miguel-osuna/Mikeduino-Microcontroller/Design Documentation/3D Models/CAPC/CAPC4564X160N EIA 1825.step

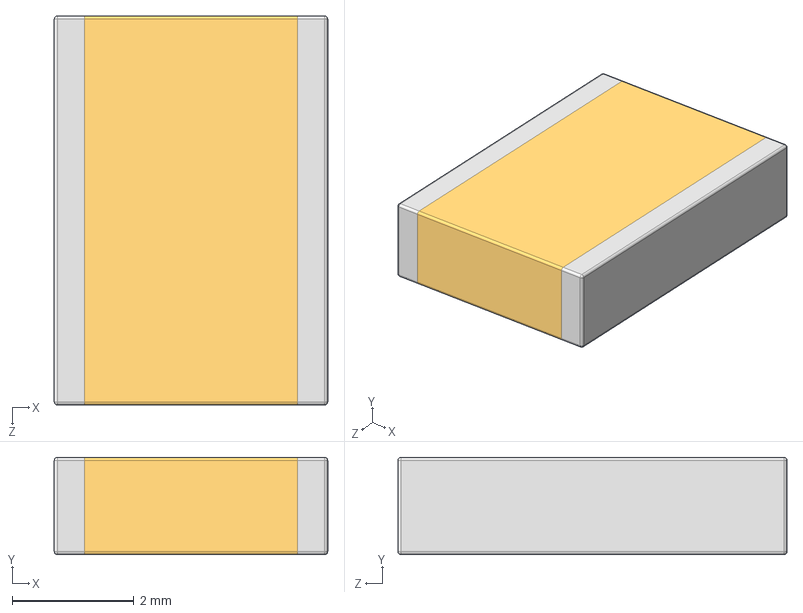
[picture p29: CAD file, 2019-04-03]
Design Documentation/3D Models/CAPC/CAPC4564X160N EIA 1825.step
4.50 x 1.60 x 6.40 mm
