miguel-osuna/Mikeduino-Microcontroller/Design Documentation/3D Models/CAPC2012X95N EIA 0805.step

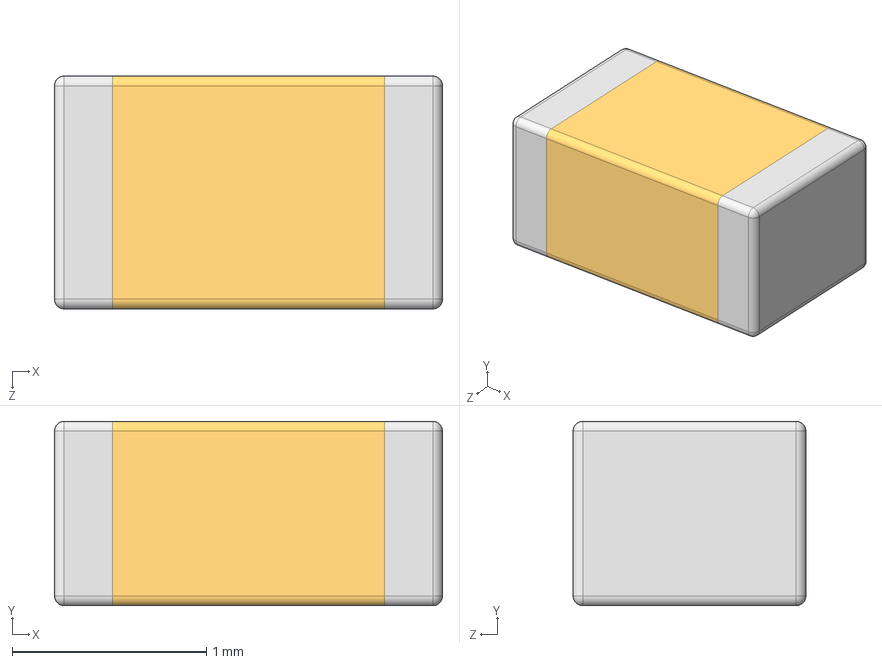
[picture p31: CAD file, 2019-04-03]
Design Documentation/3D Models/CAPC2012X95N EIA 0805.step
2.00 x 0.95 x 1.20 mm
