miguel-osuna/Mikeduino-Microcontroller/Design Documentation/3D Models/User Library-CapAluRadial_D63H70P25.step

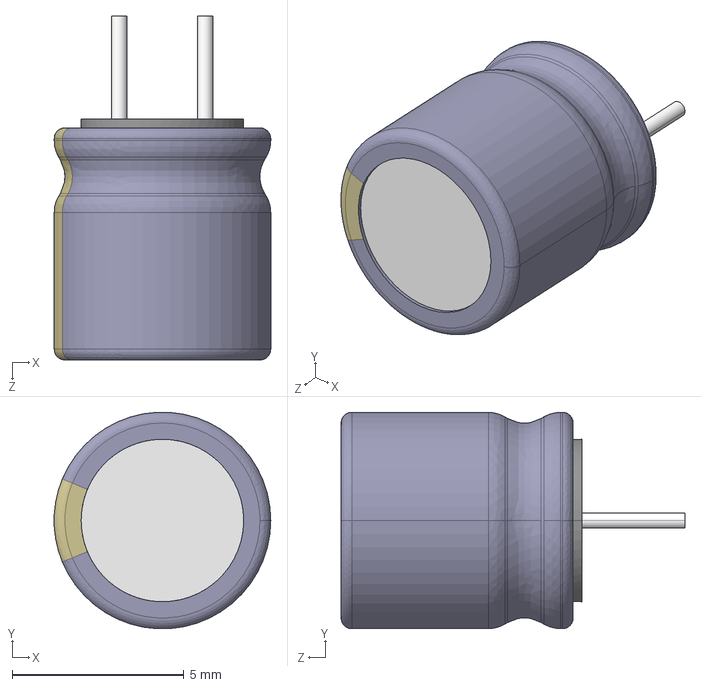
[picture p33: CAD file, 2019-04-03]
Design Documentation/3D Models/User Library-CapAluRadial_D63H70P25.step
6.30 x 6.29 x 10.0 mm
