miguel-osuna/Mikeduino-Microcontroller/Design Documentation/3D Models/HDR_1x3_White.stp

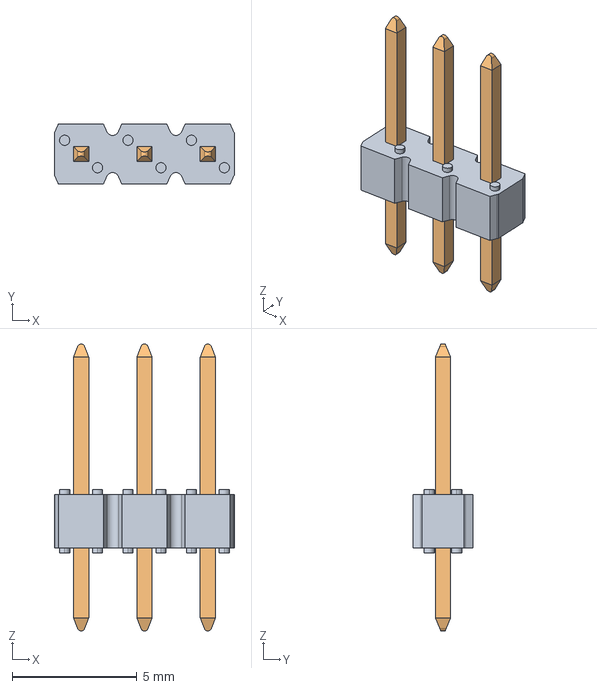
[picture p35: CAD file, 2019-04-03]
Design Documentation/3D Models/HDR_1x3_White.stp
7.22 x 2.41 x 11.5 mm
77310_Y16 x 3
