miguel-osuna/Mikeduino-Microcontroller/Design Documentation/3D Models/CAPC/CAPC4833X280N EIA 1913.step

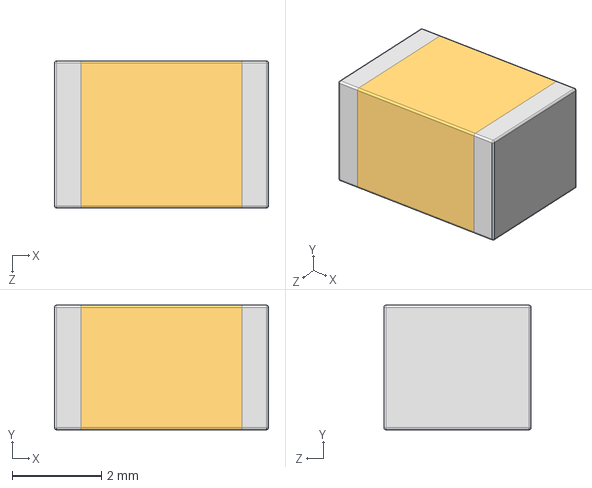
[picture p36: CAD file, 2019-04-03]
Design Documentation/3D Models/CAPC/CAPC4833X280N EIA 1913.step
4.80 x 2.80 x 3.30 mm
