miguel-osuna/Mikeduino-Microcontroller/Design Documentation/3D Models/User Library-LED SMD 0603 super red.step

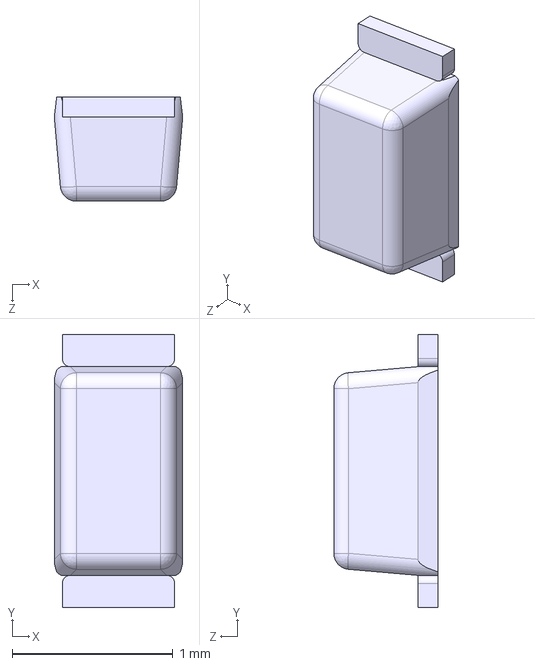
[picture p37: CAD file, 2019-04-03]
Design Documentation/3D Models/User Library-LED SMD 0603 super red.step
0.8 x 1.70 x 0.65 mm
