miguel-osuna/Mikeduino-Microcontroller/Design Documentation/3D Models/dil_socket.stp

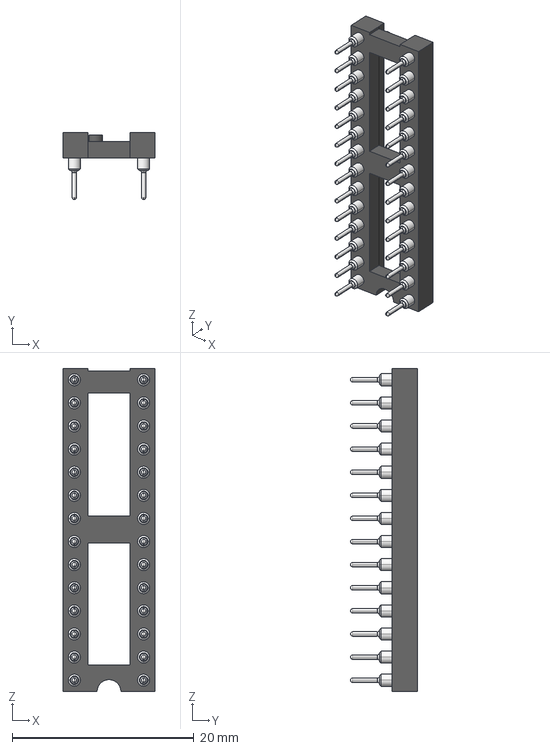
[picture p39: CAD file, 2019-04-03]
Design Documentation/3D Models/dil_socket.stp
10.1 x 7.37 x 35.5 mm
