miguel-osuna/Mikeduino-Microcontroller/Design Documentation/3D Models/HDR_1x4_White.stp

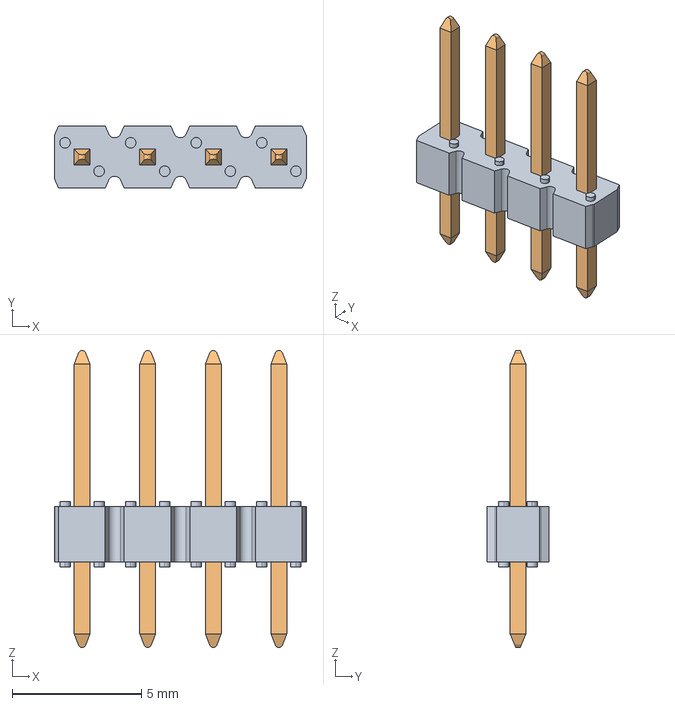
[picture p41: CAD file, 2019-04-03]
Design Documentation/3D Models/HDR_1x4_White.stp
9.76 x 2.41 x 11.5 mm
