miguel-osuna/Mikeduino-Microcontroller/Design Documentation/3D Models/R0603.step

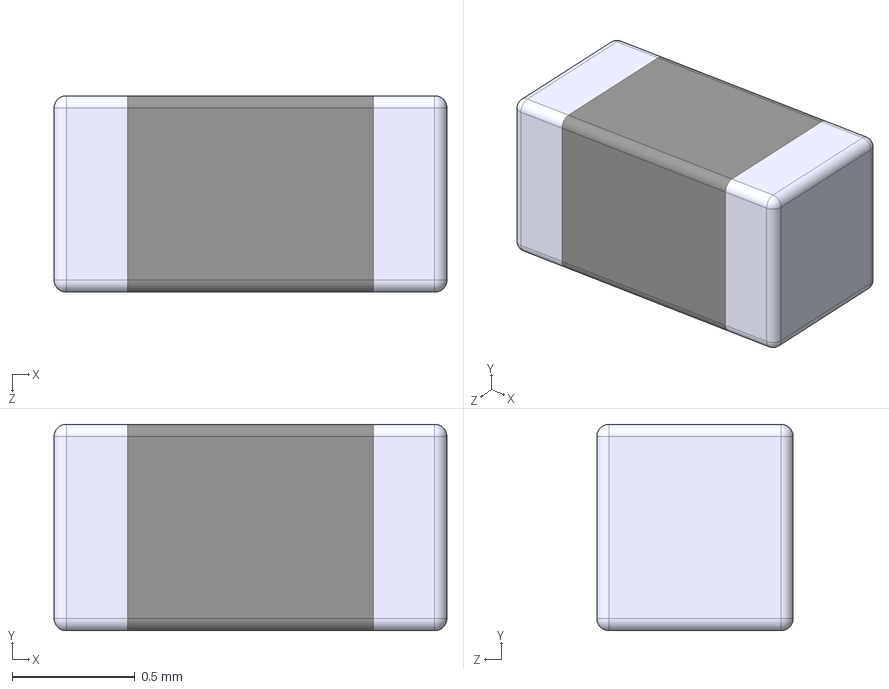
[picture p43: CAD file, 2019-04-03]
Design Documentation/3D Models/R0603.step
1.60 x 0.84 x 0.8 mm
