miguel-osuna/Mikeduino-Microcontroller/Design Documentation/3D Models/CAPC/CAPC3216X125N EIA 1206.step

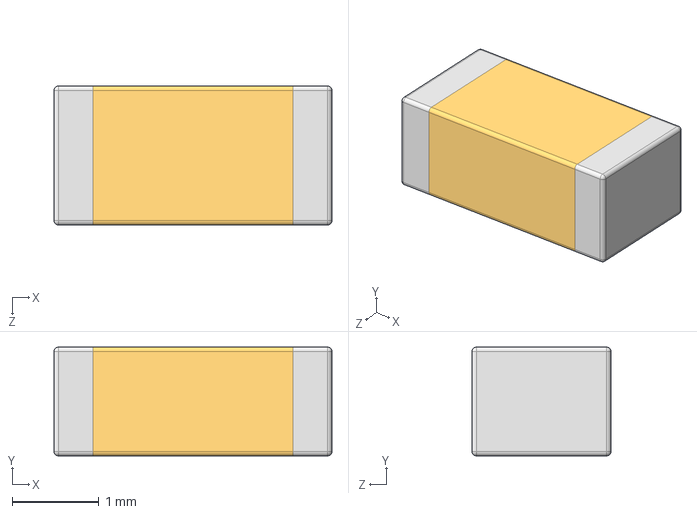
[picture p48: CAD file, 2019-04-03]
Design Documentation/3D Models/CAPC/CAPC3216X125N EIA 1206.step
3.20 x 1.25 x 1.60 mm
