miguel-osuna/Mikeduino-Microcontroller/Design Documentation/3D Models/CAPC/CAPC6332X71N EIA 2512.step

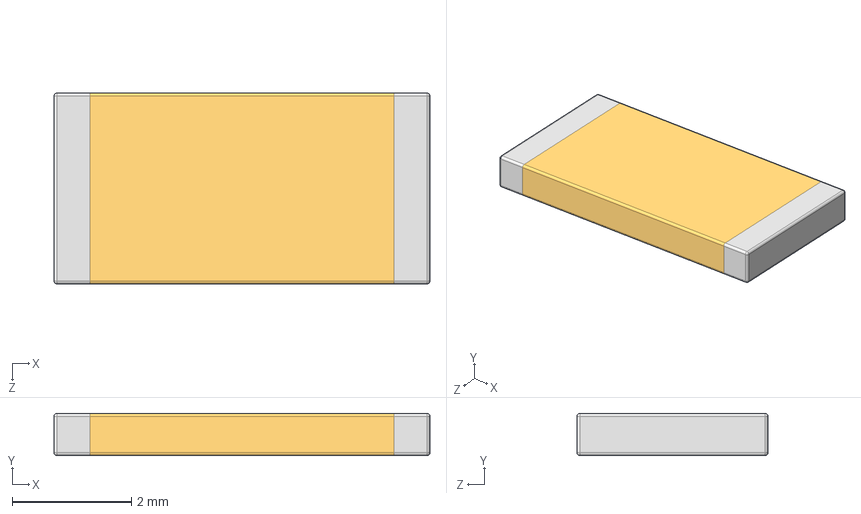
[picture p49: CAD file, 2019-04-03]
Design Documentation/3D Models/CAPC/CAPC6332X71N EIA 2512.step
6.30 x 0.71 x 3.20 mm
