miguel-osuna/Mikeduino-Microcontroller/Design Documentation/3D Models/CAPC/CAPC4612X140N CDR02.step

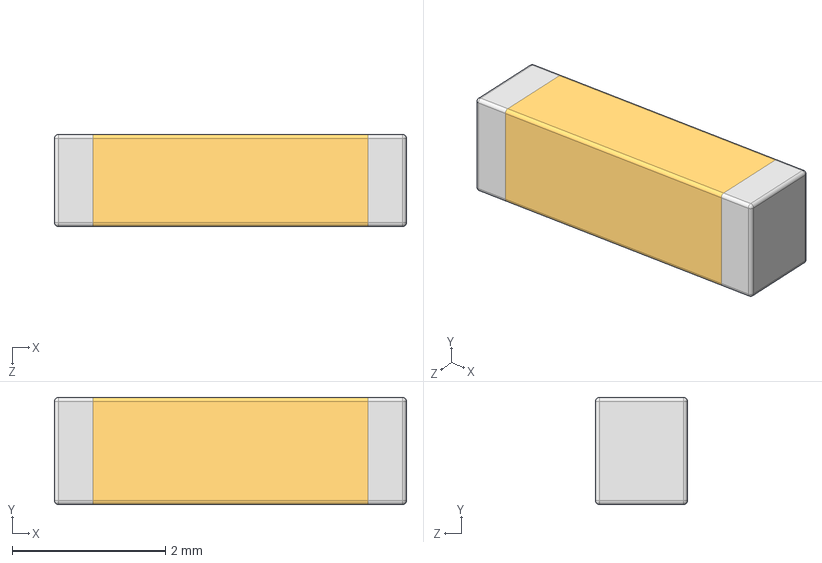
[picture p50: CAD file, 2019-04-03]
Design Documentation/3D Models/CAPC/CAPC4612X140N CDR02.step
4.60 x 1.40 x 1.20 mm
