miguel-osuna/Mikeduino-Microcontroller/Design Documentation/3D Models/CAPC/CAPC0816X61N EIA 0363.step

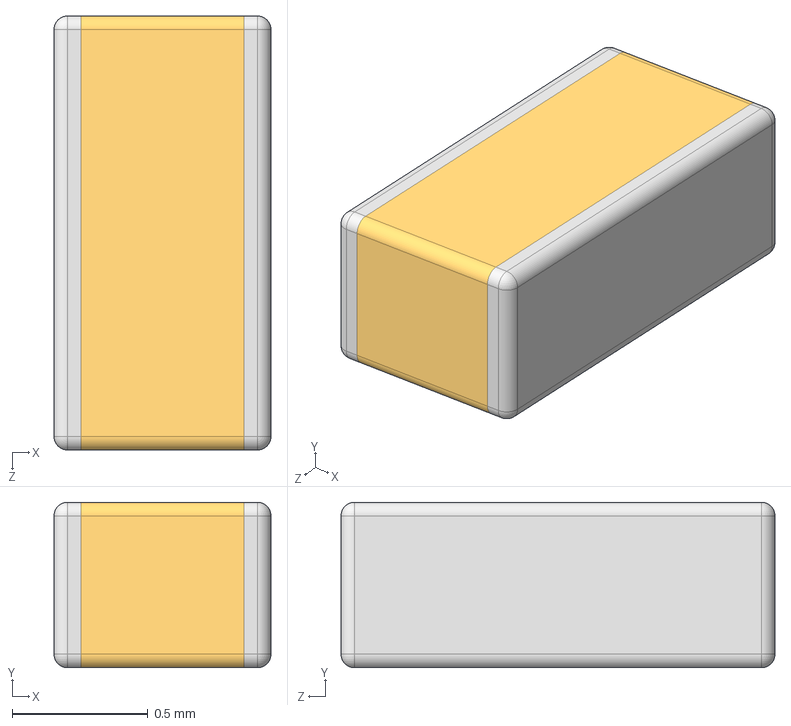
[picture p53: CAD file, 2019-04-03]
Design Documentation/3D Models/CAPC/CAPC0816X61N EIA 0363.step
0.8 x 0.61 x 1.60 mm
