miguel-osuna/Mikeduino-Microcontroller/Design Documentation/3D Models/CAPC/CAPC4520X130N EIA 1807.step

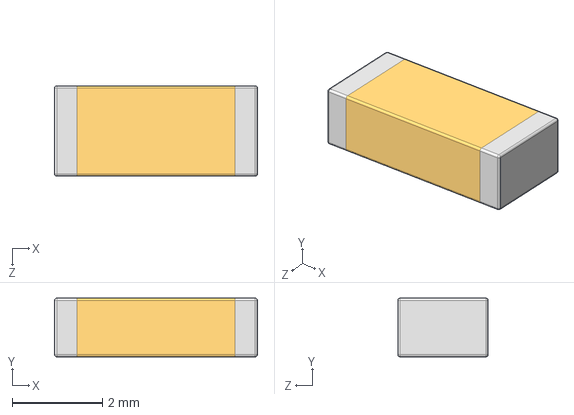
[picture p57: CAD file, 2019-04-03]
Design Documentation/3D Models/CAPC/CAPC4520X130N EIA 1807.step
4.50 x 1.30 x 2.00 mm
