miguel-osuna/Mikeduino-Microcontroller/Design Documentation/3D Models/CAPC/CAPC4564X218N EIA 1825.step

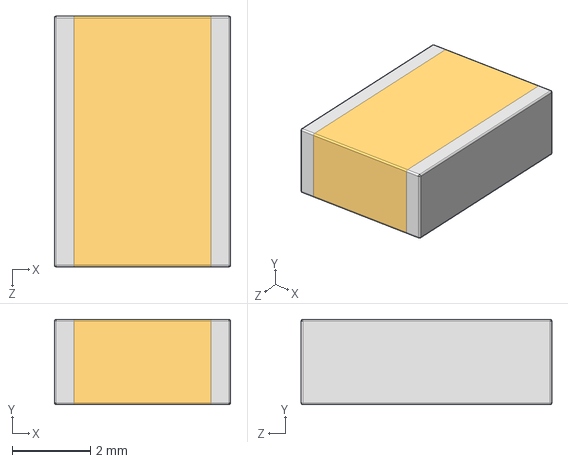
[picture p58: CAD file, 2019-04-03]
Design Documentation/3D Models/CAPC/CAPC4564X218N EIA 1825.step
4.50 x 2.18 x 6.40 mm
