miguel-osuna/Mikeduino-Microcontroller/Design Documentation/3D Models/CAPC/CAPC1005X60N EIA 0402.step

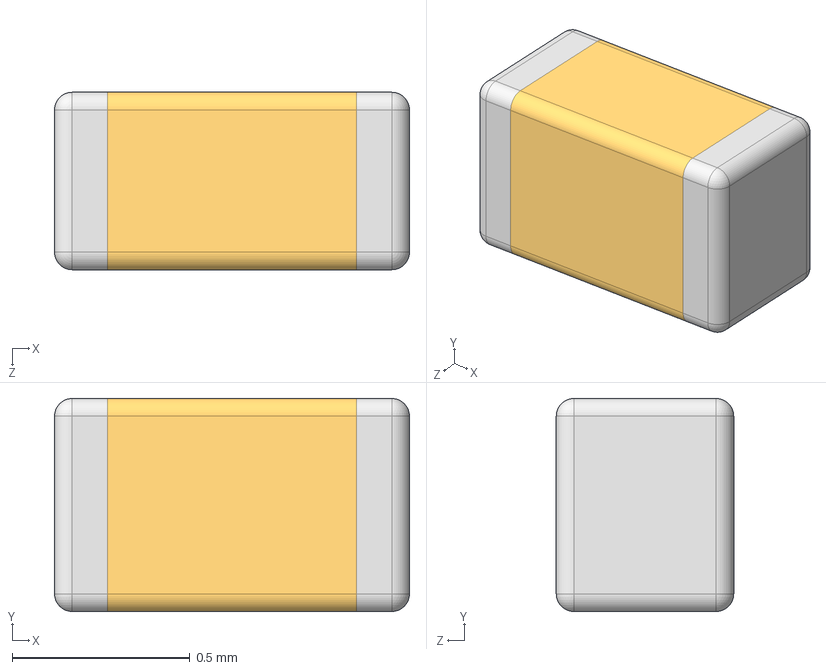
[picture p60: CAD file, 2019-04-03]
Design Documentation/3D Models/CAPC/CAPC1005X60N EIA 0402.step
1.00 x 0.6 x 0.5 mm
