miguel-osuna/Mikeduino-Microcontroller/Design Documentation/3D Models/CAPC/CAPC5650X145N EIA 2220.step

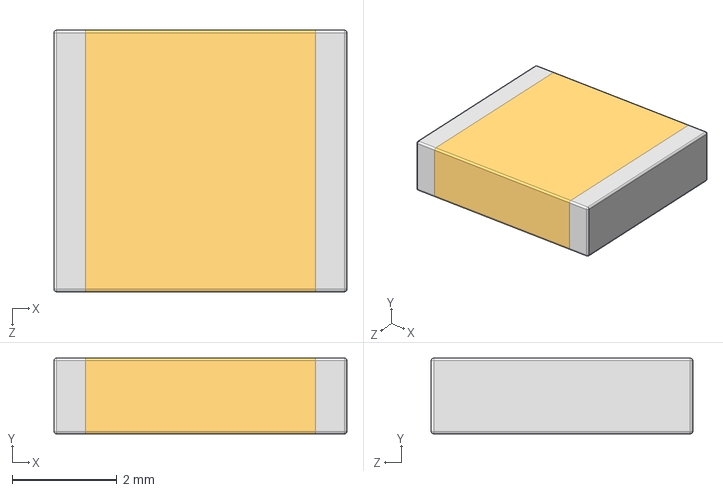
[picture p63: CAD file, 2019-04-03]
Design Documentation/3D Models/CAPC/CAPC5650X145N EIA 2220.step
5.60 x 1.45 x 5.00 mm
