miguel-osuna/Mikeduino-Microcontroller/Design Documentation/3D Models/CAPC/CAPC1608X92N EIA 0603.step

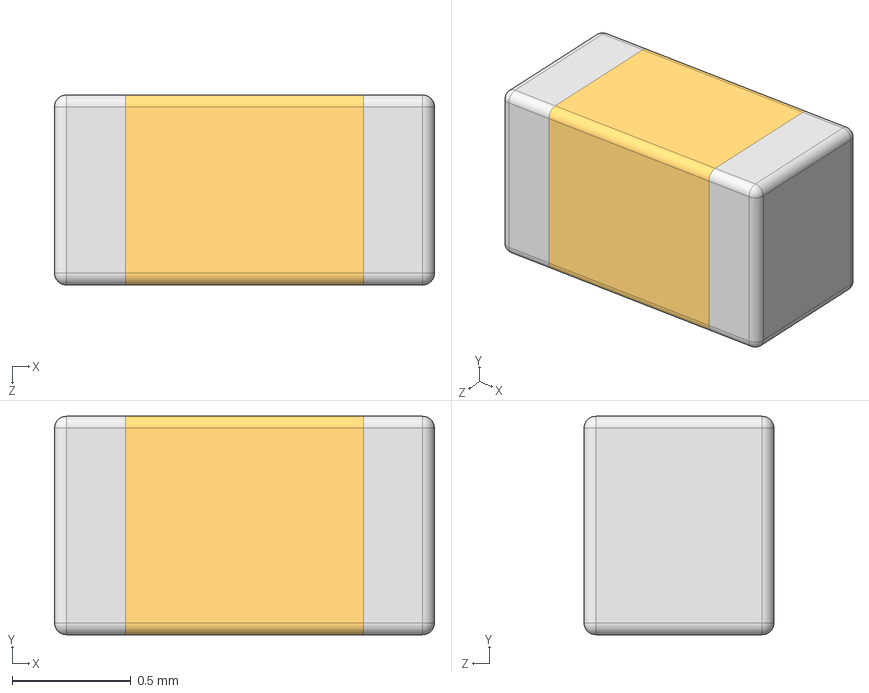
[picture p64: CAD file, 2019-04-03]
Design Documentation/3D Models/CAPC/CAPC1608X92N EIA 0603.step
1.60 x 0.92 x 0.8 mm
