miguel-osuna/Mikeduino-Microcontroller/Design Documentation/3D Models/CAPC/CAPC5025X71N EIA 2010.step

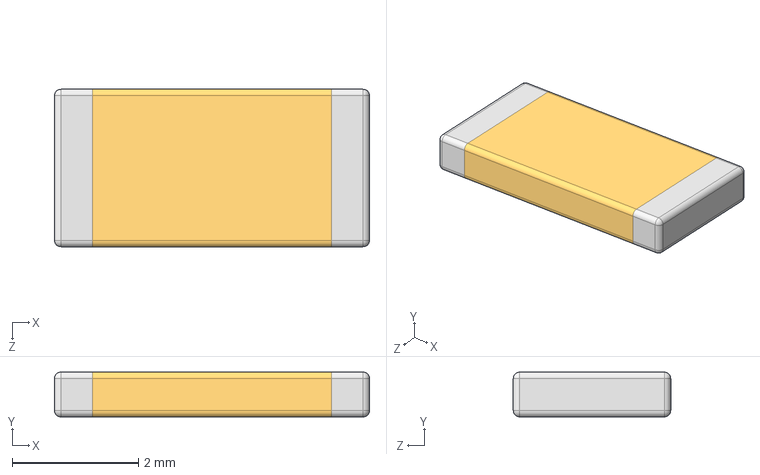
[picture p67: CAD file, 2019-04-03]
Design Documentation/3D Models/CAPC/CAPC5025X71N EIA 2010.step
5.00 x 0.71 x 2.50 mm
