miguel-osuna/Mikeduino-Microcontroller/Design Documentation/3D Models/CAPC/CAPC1632X76N EIA 0612.step

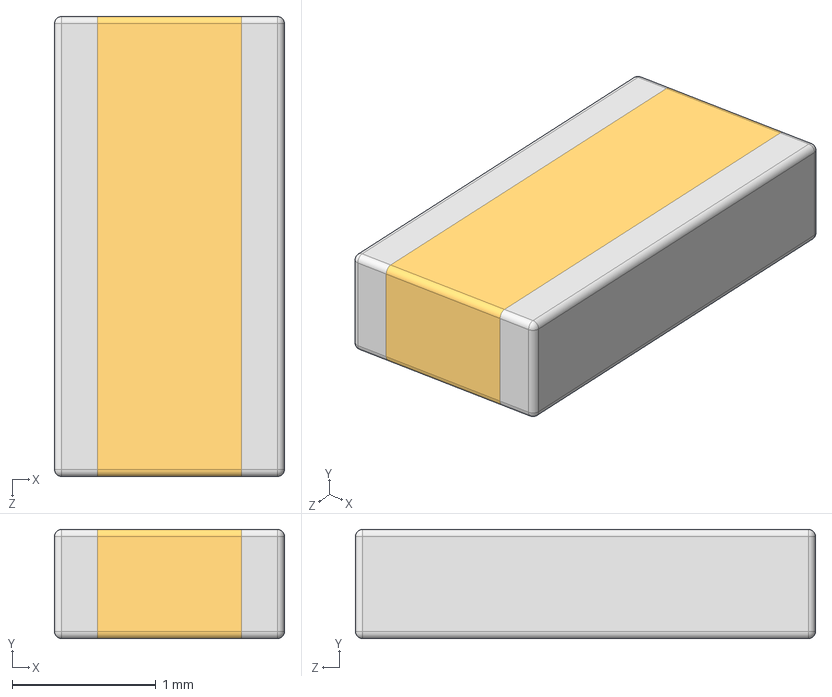
[picture p68: CAD file, 2019-04-03]
Design Documentation/3D Models/CAPC/CAPC1632X76N EIA 0612.step
1.60 x 0.76 x 3.20 mm
