miguel-osuna/Mikeduino-Microcontroller/Design Documentation/3D Models/CAPC/CAPC6041X320N EIA 2220.step

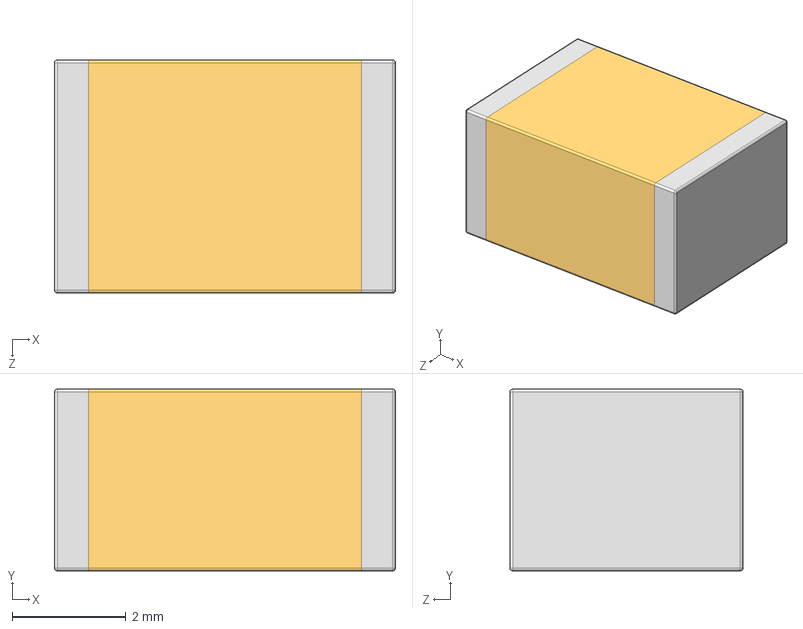
[picture p70: CAD file, 2019-04-03]
Design Documentation/3D Models/CAPC/CAPC6041X320N EIA 2220.step
6.00 x 3.20 x 4.10 mm
