miguel-osuna/Mikeduino-Microcontroller/Design Documentation/3D Models/CAPC/CAPC5750X279N EIA 2220.step

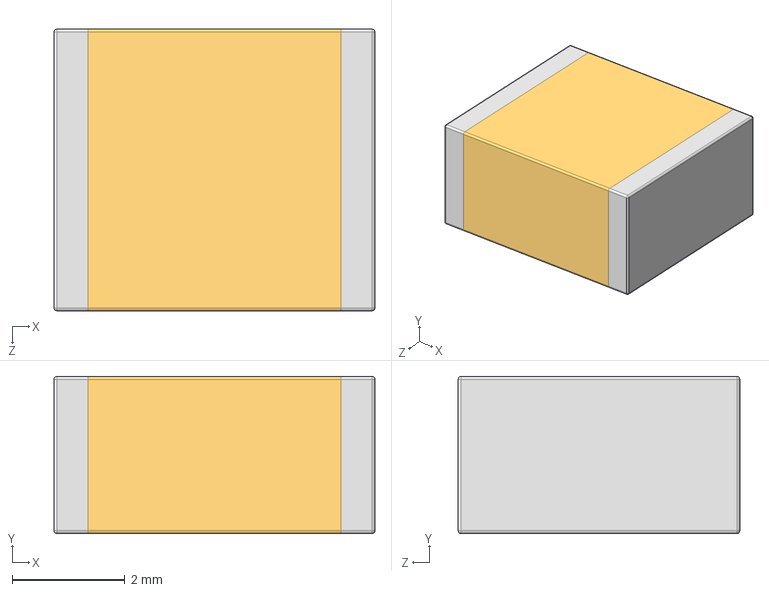
[picture p77: CAD file, 2019-04-03]
Design Documentation/3D Models/CAPC/CAPC5750X279N EIA 2220.step
5.70 x 2.79 x 5.00 mm
