miguel-osuna/Mikeduino-Microcontroller/Design Documentation/3D Models/CAPC/CAPC4520X168N EIA 1808.step

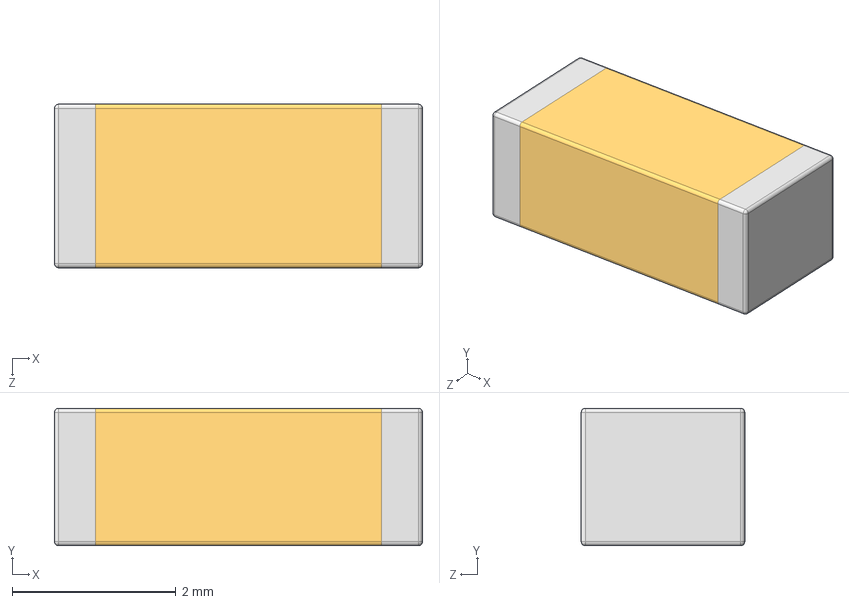
[picture p78: CAD file, 2019-04-03]
Design Documentation/3D Models/CAPC/CAPC4520X168N EIA 1808.step
4.50 x 1.68 x 2.00 mm
