miguel-osuna/Mikeduino-Microcontroller/Design Documentation/3D Models/CAPC/CAPC5663X115N EIA 2225.step

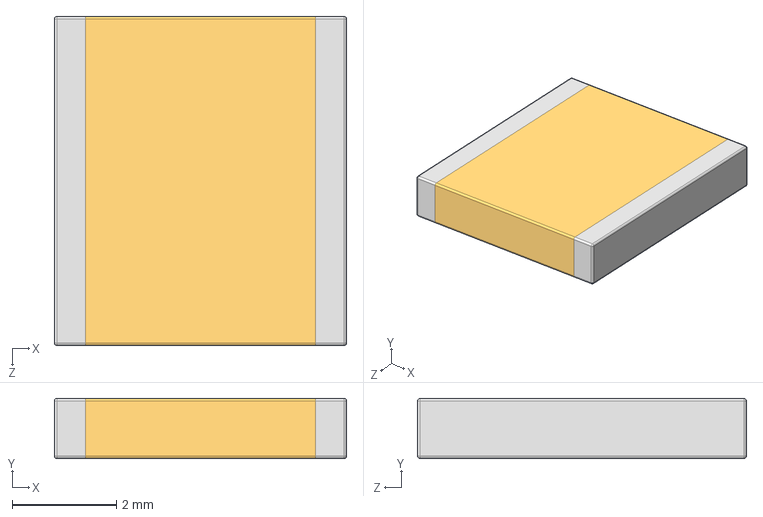
[picture p80: CAD file, 2019-04-03]
Design Documentation/3D Models/CAPC/CAPC5663X115N EIA 2225.step
5.60 x 1.15 x 6.30 mm
