miguel-osuna/Mikeduino-Microcontroller/Design Documentation/3D Models/CAPC/CAPC5651X218N EIA 2220.step

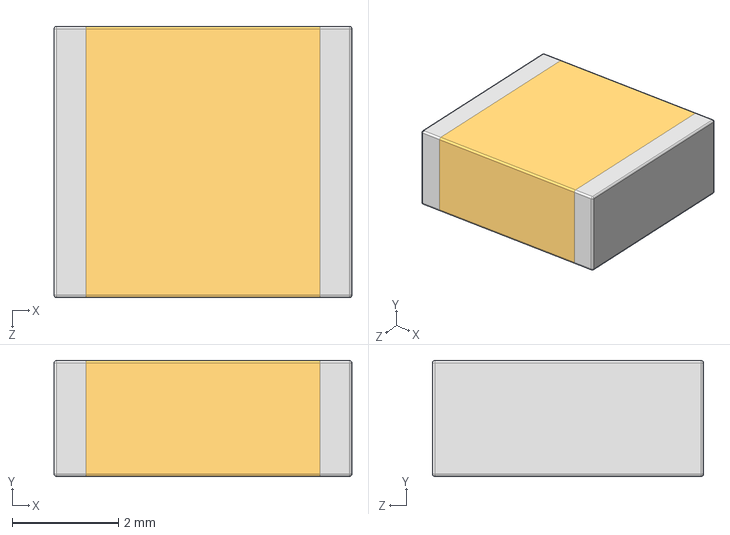
[picture p81: CAD file, 2019-04-03]
Design Documentation/3D Models/CAPC/CAPC5651X218N EIA 2220.step
5.60 x 2.18 x 5.10 mm
