miguel-osuna/Mikeduino-Microcontroller/Design Documentation/3D Models/CAPC/CAPC1608X55N EIA 0603.step

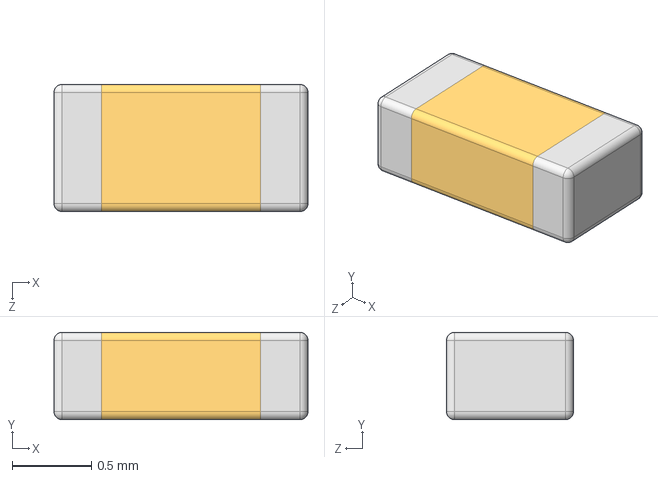
[picture p82: CAD file, 2019-04-03]
Design Documentation/3D Models/CAPC/CAPC1608X55N EIA 0603.step
1.60 x 0.55 x 0.8 mm
