miguel-osuna/Mikeduino-Microcontroller/Design Documentation/3D Models/CAPC/CAPC3225X100N EIA 1210.step

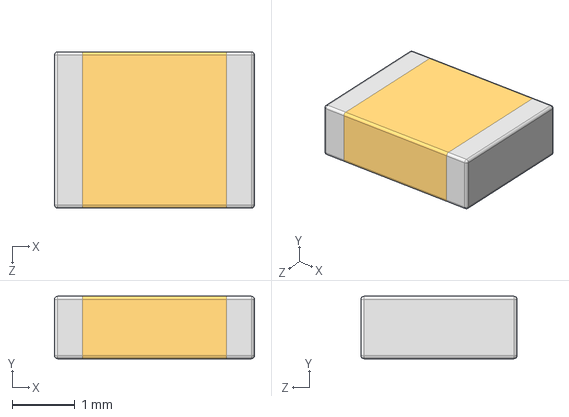
[picture p86: CAD file, 2019-04-03]
Design Documentation/3D Models/CAPC/CAPC3225X100N EIA 1210.step
3.20 x 1.00 x 2.50 mm
