miguel-osuna/Mikeduino-Microcontroller/Design Documentation/3D Models/CAPC/CAPC1320X76N EIA 0508.step

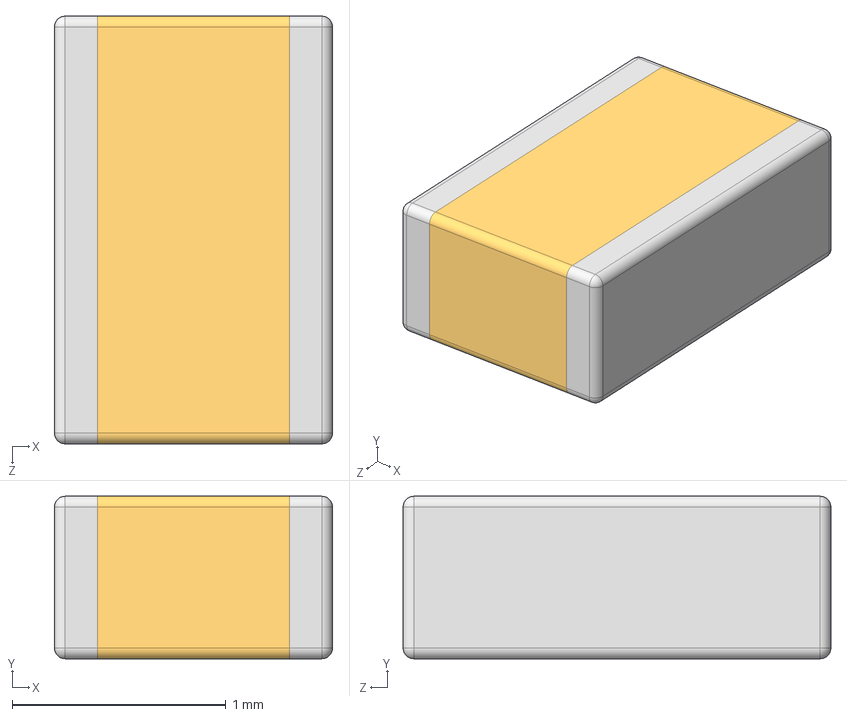
[picture p88: CAD file, 2019-04-03]
Design Documentation/3D Models/CAPC/CAPC1320X76N EIA 0508.step
1.30 x 0.76 x 2.00 mm
