miguel-osuna/Mikeduino-Microcontroller/Design Documentation/3D Models/CAPC/CAPC1608X95N EIA 0603.step

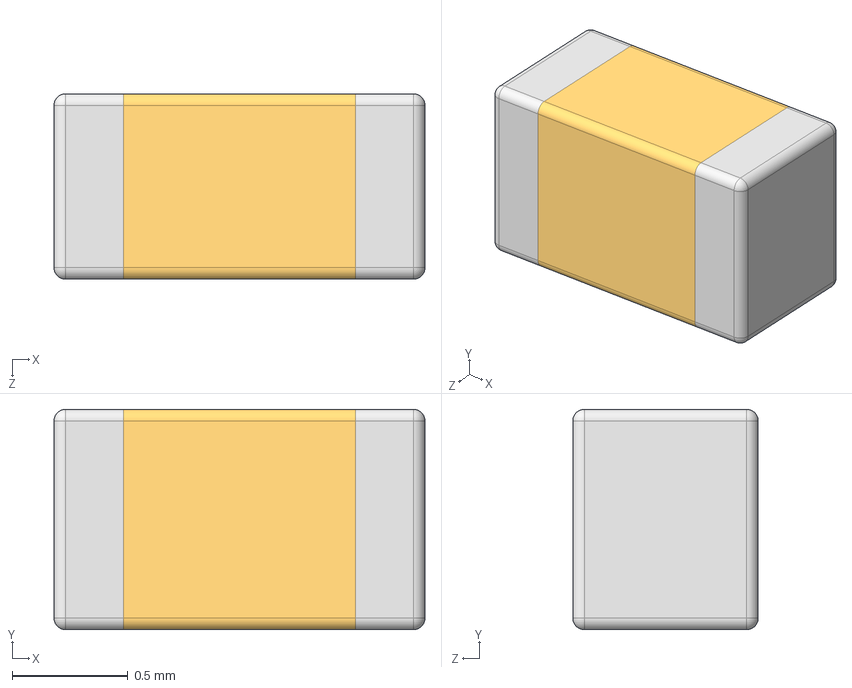
[picture p90: CAD file, 2019-04-03]
Design Documentation/3D Models/CAPC/CAPC1608X95N EIA 0603.step
1.60 x 0.95 x 0.8 mm
