miguel-osuna/Mikeduino-Microcontroller/Design Documentation/3D Models/CAPC/CAPC1005X55N EIA 0402.step

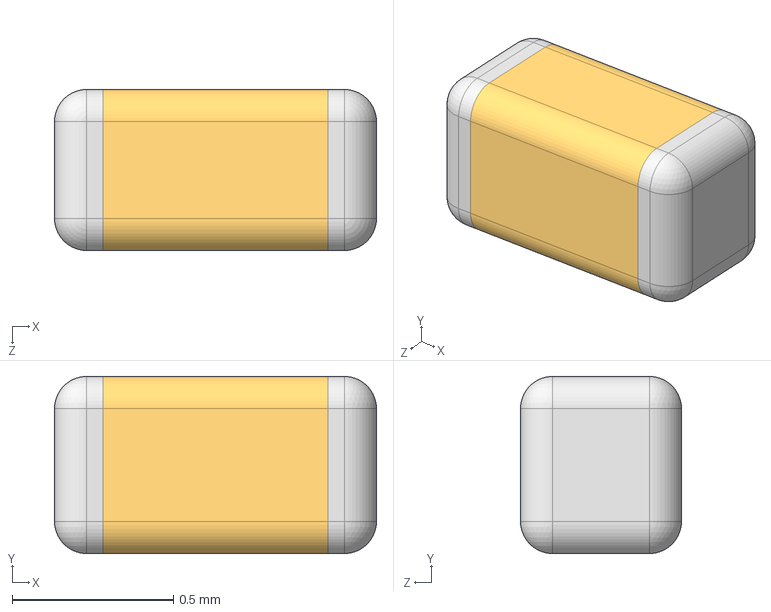
[picture p93: CAD file, 2019-04-03]
Design Documentation/3D Models/CAPC/CAPC1005X55N EIA 0402.step
1.00 x 0.55 x 0.5 mm
