miguel-osuna/Mikeduino-Microcontroller/Design Documentation/3D Models/CAPC/CAPC2012X90N EIA 0805.step

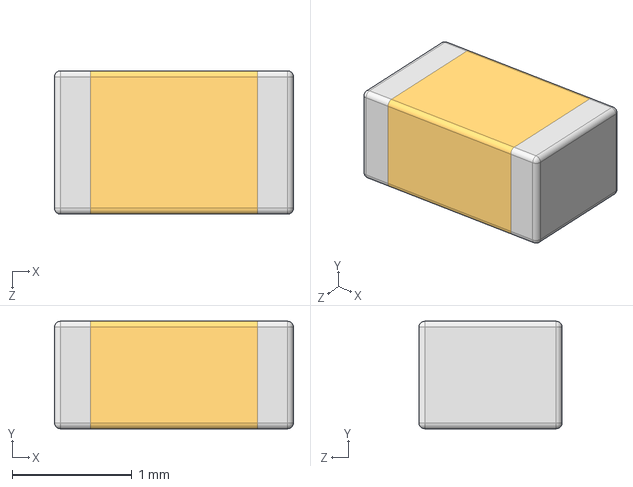
[picture p96: CAD file, 2019-04-03]
Design Documentation/3D Models/CAPC/CAPC2012X90N EIA 0805.step
2.00 x 0.9 x 1.20 mm
