miguel-osuna/Mikeduino-Microcontroller/Design Documentation/3D Models/CAPC/CAPC4665X150N CDR35.step

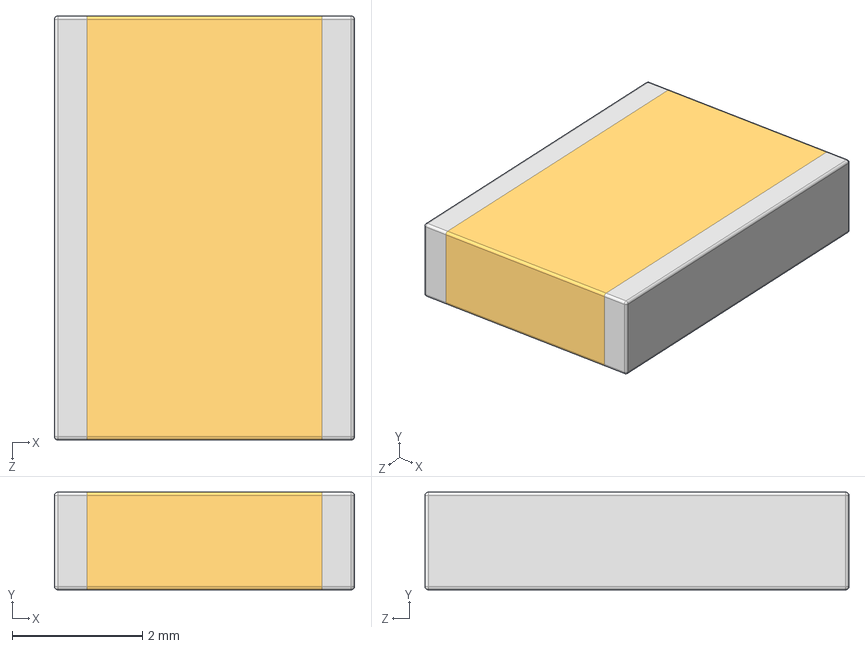
[picture p97: CAD file, 2019-04-03]
Design Documentation/3D Models/CAPC/CAPC4665X150N CDR35.step
4.60 x 1.50 x 6.50 mm
