miguel-osuna/Mikeduino-Microcontroller/Design Documentation/3D Models/CAPC/CAPC1508X65N EIA 0603.step

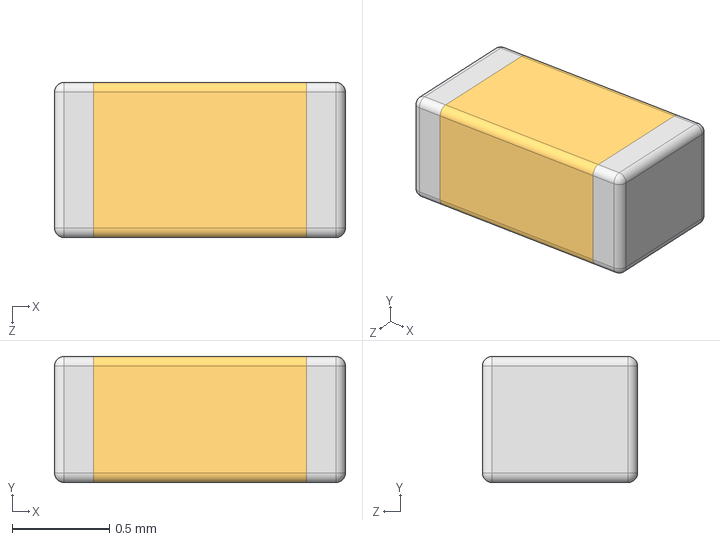
[picture p99: CAD file, 2019-04-03]
Design Documentation/3D Models/CAPC/CAPC1508X65N EIA 0603.step
1.50 x 0.65 x 0.8 mm
