miguel-osuna/Mikeduino-Microcontroller/Design Documentation/3D Models/CAPC/CAPC5663X125N EIA 2225.step

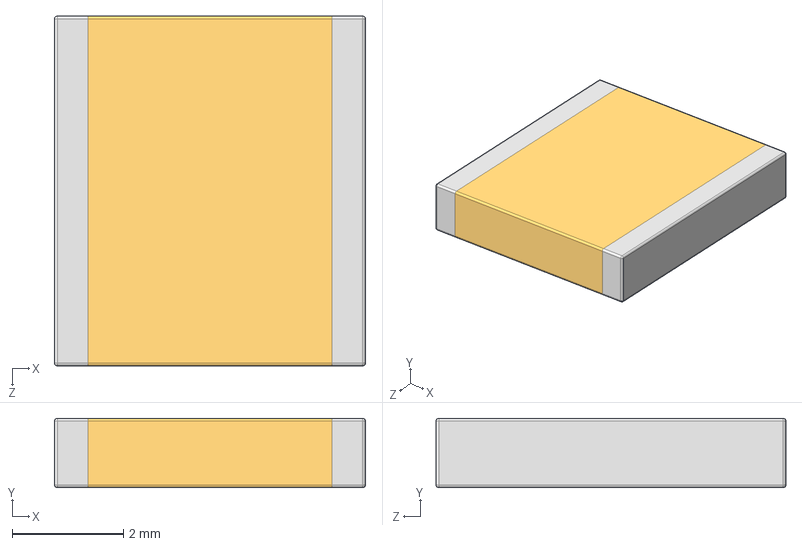
[picture p100: CAD file, 2019-04-03]
Design Documentation/3D Models/CAPC/CAPC5663X125N EIA 2225.step
5.60 x 1.25 x 6.30 mm
