miguel-osuna/Mikeduino-Microcontroller/Design Documentation/3D Models/CAPC/CAPC3225X150N CDR33.step

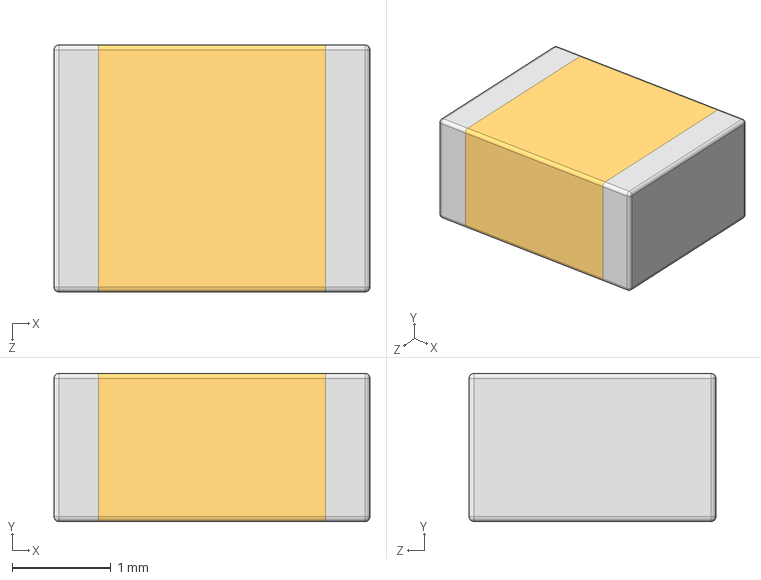
[picture p103: CAD file, 2019-04-03]
Design Documentation/3D Models/CAPC/CAPC3225X150N CDR33.step
3.20 x 1.50 x 2.50 mm
