miguel-osuna/Mikeduino-Microcontroller/Design Documentation/3D Models/CAPC/CAPC2012X71N EIA 0805.step

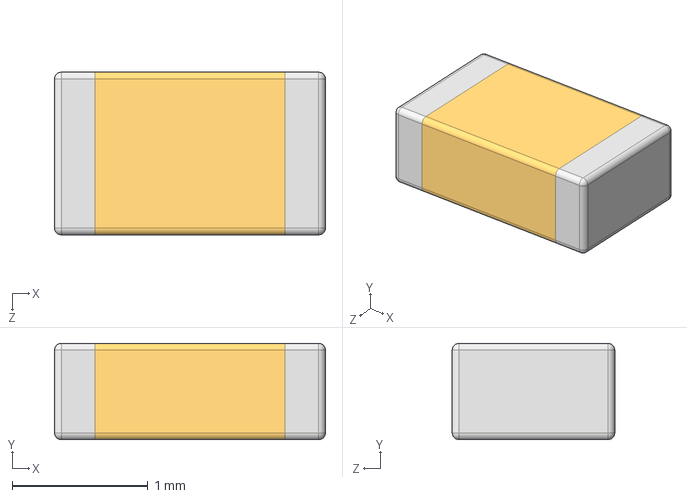
[picture p105: CAD file, 2019-04-03]
Design Documentation/3D Models/CAPC/CAPC2012X71N EIA 0805.step
2.00 x 0.71 x 1.20 mm
