miguel-osuna/Mikeduino-Microcontroller/Design Documentation/3D Models/CAPC/CAPC4620X203N CDR03.step

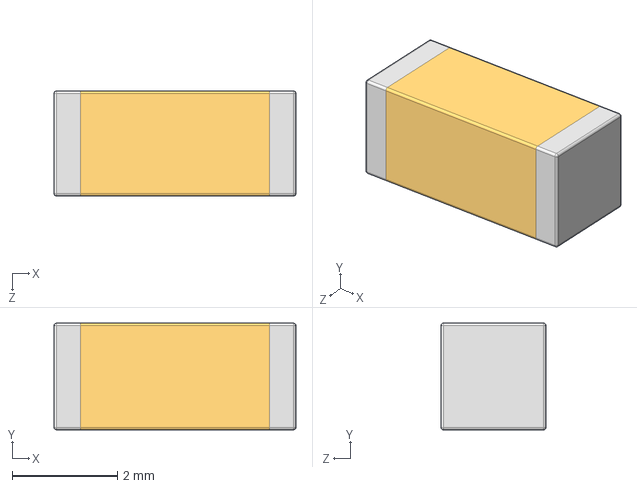
[picture p107: CAD file, 2019-04-03]
Design Documentation/3D Models/CAPC/CAPC4620X203N CDR03.step
4.60 x 2.03 x 2.00 mm
