miguel-osuna/Mikeduino-Microcontroller/Design Documentation/3D Models/CAPC/CAPC4564X130N EIA 1825.step

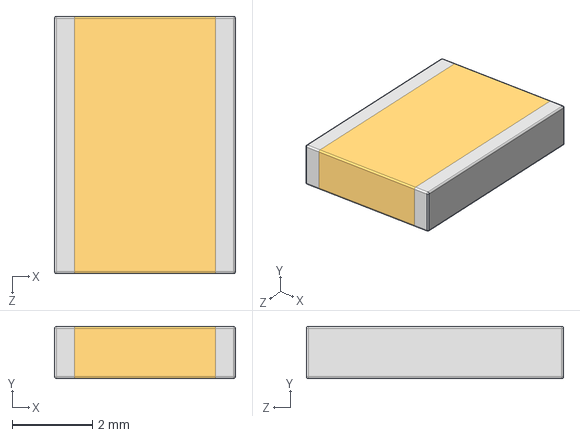
[picture p108: CAD file, 2019-04-03]
Design Documentation/3D Models/CAPC/CAPC4564X130N EIA 1825.step
4.50 x 1.30 x 6.40 mm
