miguel-osuna/Mikeduino-Microcontroller/Design Documentation/3D Models/CAPC/CAPC1005X56N EIA 0402.step

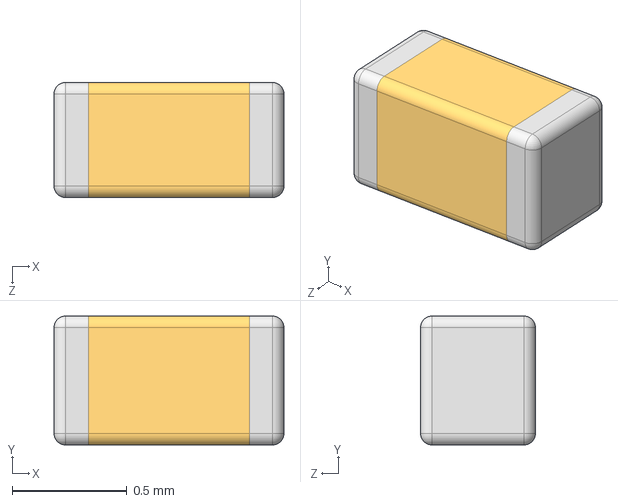
[picture p110: CAD file, 2019-04-03]
Design Documentation/3D Models/CAPC/CAPC1005X56N EIA 0402.step
1.00 x 0.56 x 0.5 mm
