miguel-osuna/Mikeduino-Microcontroller/Design Documentation/3D Models/CAPC/CAPC4664X203N CDR05.step

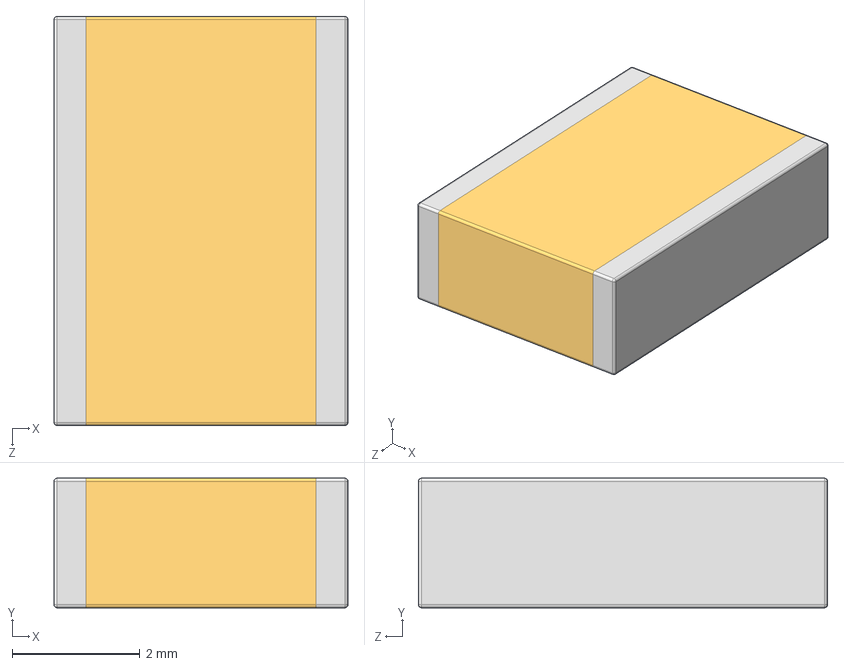
[picture p112: CAD file, 2019-04-03]
Design Documentation/3D Models/CAPC/CAPC4664X203N CDR05.step
4.60 x 2.03 x 6.40 mm
