miguel-osuna/Mikeduino-Microcontroller/Design Documentation/3D Models/CAPC/CAPC5664X200N EIA 2225.step

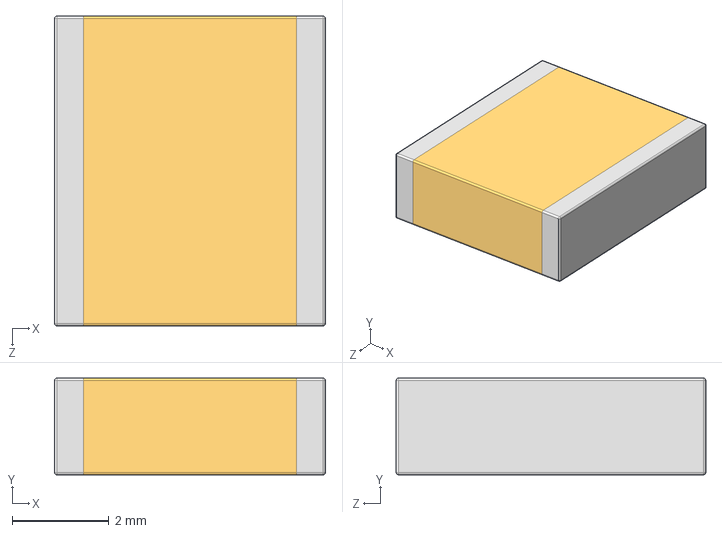
[picture p113: CAD file, 2019-04-03]
Design Documentation/3D Models/CAPC/CAPC5664X200N EIA 2225.step
5.60 x 2.00 x 6.40 mm
