miguel-osuna/Mikeduino-Microcontroller/Design Documentation/3D Models/CAPC/CAPC3813X130N EIA 1505.step

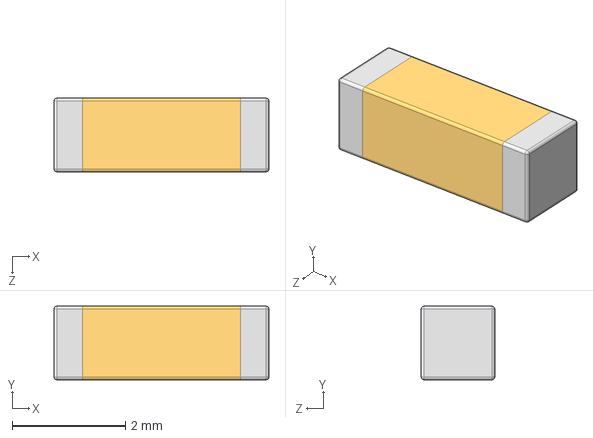
[picture p120: CAD file, 2019-04-03]
Design Documentation/3D Models/CAPC/CAPC3813X130N EIA 1505.step
3.80 x 1.30 x 1.30 mm
