miguel-osuna/Mikeduino-Microcontroller/Design Documentation/3D Models/CAPC/CAPC3225X279N EIA 1210.step

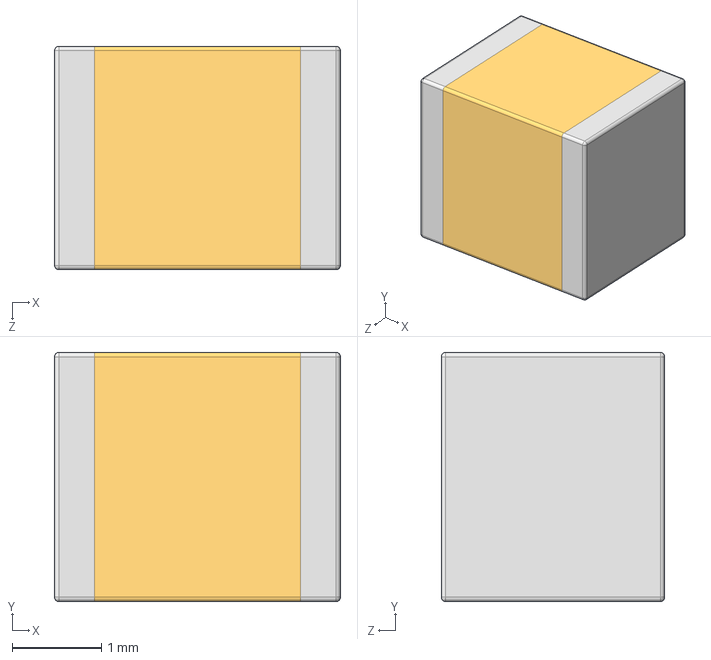
[picture p122: CAD file, 2019-04-03]
Design Documentation/3D Models/CAPC/CAPC3225X279N EIA 1210.step
3.20 x 2.79 x 2.50 mm
