miguel-osuna/Mikeduino-Microcontroller/Design Documentation/3D Models/CAPC/CAPC0603X33N EIA 2220.step

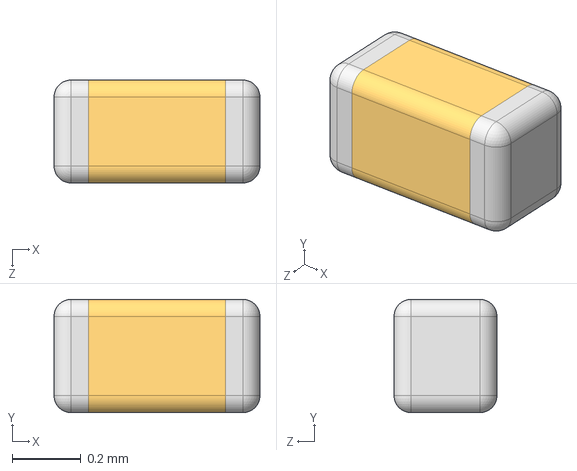
[picture p123: CAD file, 2019-04-03]
Design Documentation/3D Models/CAPC/CAPC0603X33N EIA 2220.step
0.6 x 0.33 x 0.3 mm
