miguel-osuna/Mikeduino-Microcontroller/Design Documentation/3D Models/CAPC/CAPC3215X168N EIA 1206.step

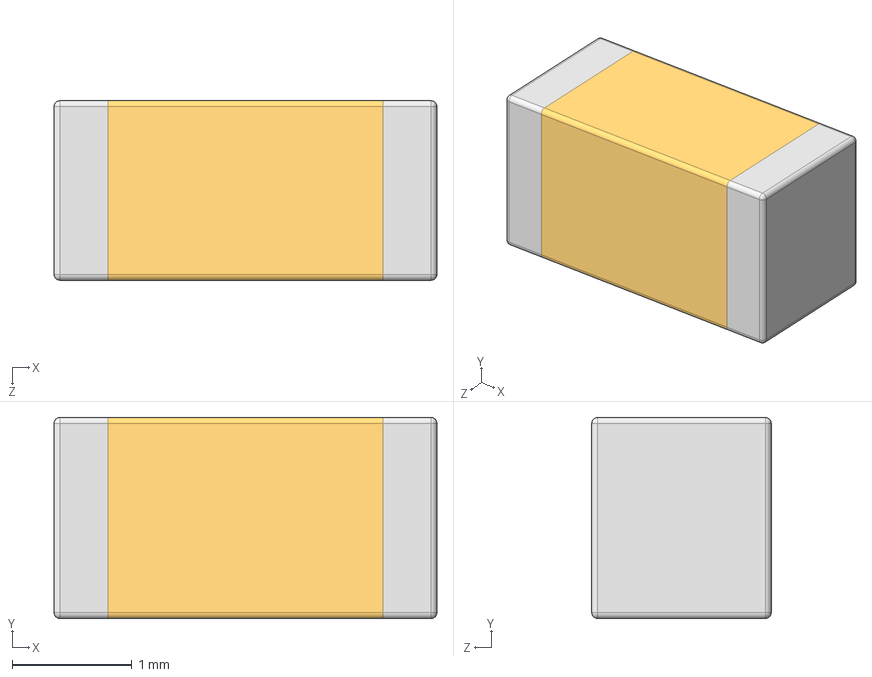
[picture p125: CAD file, 2019-04-03]
Design Documentation/3D Models/CAPC/CAPC3215X168N EIA 1206.step
3.20 x 1.68 x 1.50 mm
