miguel-osuna/Mikeduino-Microcontroller/Design Documentation/3D Models/CAPC/CAPC1632X168N EIA 0612.step

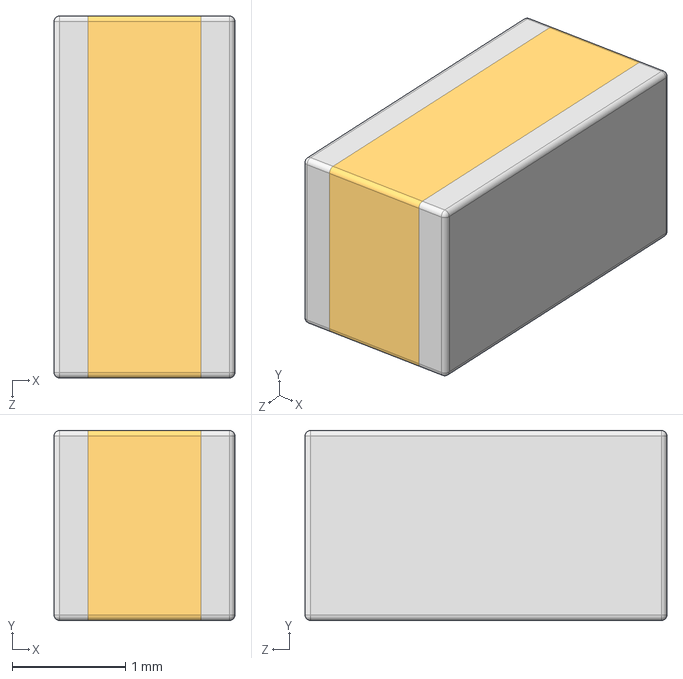
[picture p126: CAD file, 2019-04-03]
Design Documentation/3D Models/CAPC/CAPC1632X168N EIA 0612.step
1.60 x 1.68 x 3.20 mm
