miguel-osuna/Mikeduino-Microcontroller/Design Documentation/3D Models/CAPC/CAPC2012X120N EIA 0805.step

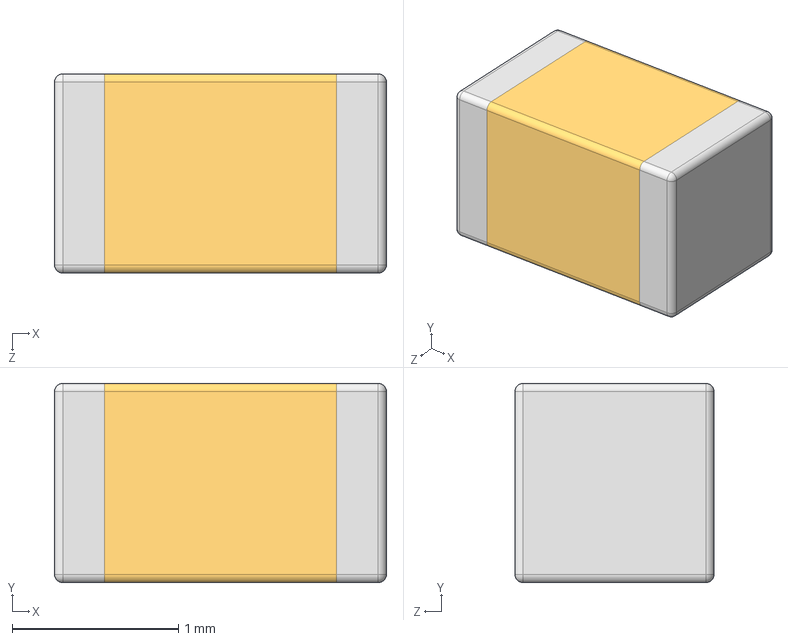
[picture p128: CAD file, 2019-04-03]
Design Documentation/3D Models/CAPC/CAPC2012X120N EIA 0805.step
2.00 x 1.20 x 1.20 mm
