miguel-osuna/Mikeduino-Microcontroller/Design Documentation/3D Models/CAPC/CAPC5664X218N EIA 2225.step

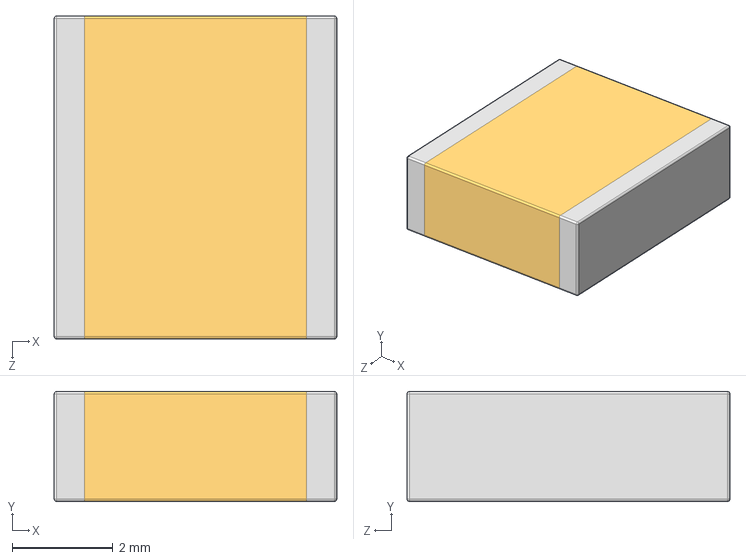
[picture p129: CAD file, 2019-04-03]
Design Documentation/3D Models/CAPC/CAPC5664X218N EIA 2225.step
5.60 x 2.18 x 6.40 mm
