miguel-osuna/Mikeduino-Microcontroller/Design Documentation/3D Models/CAPC/CAPC1220X107N EIA 0508.step

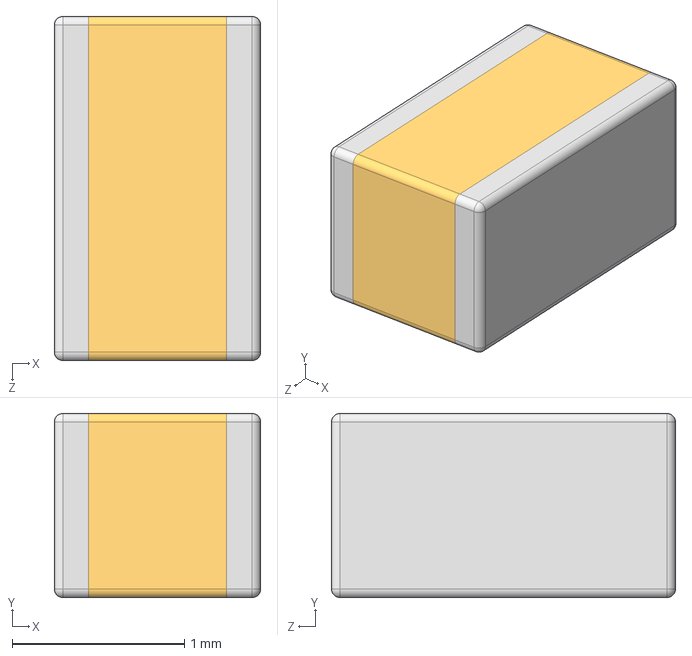
[picture p131: CAD file, 2019-04-03]
Design Documentation/3D Models/CAPC/CAPC1220X107N EIA 0508.step
1.20 x 1.07 x 2.00 mm
