miguel-osuna/Mikeduino-Microcontroller/Design Documentation/3D Models/CAPC/CAPC5764X152N EIA 2225.step

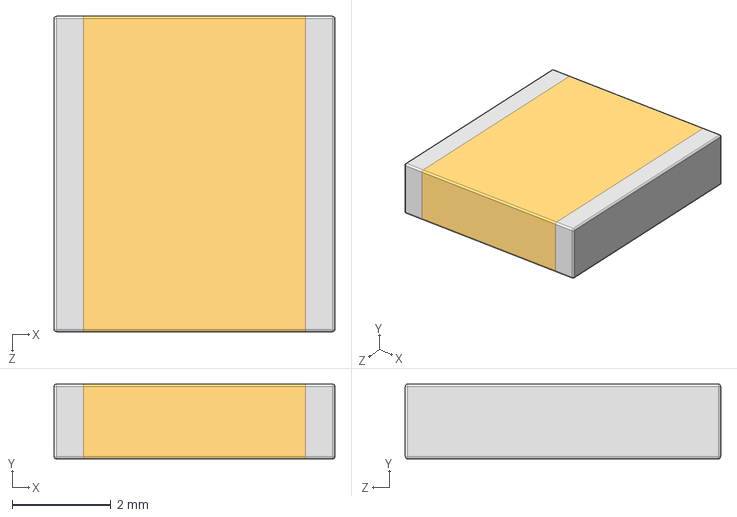
[picture p132: CAD file, 2019-04-03]
Design Documentation/3D Models/CAPC/CAPC5764X152N EIA 2225.step
5.70 x 1.52 x 6.40 mm
