miguel-osuna/Mikeduino-Microcontroller/Design Documentation/3D Models/CAPC/CAPC4632X203N CDR04.step

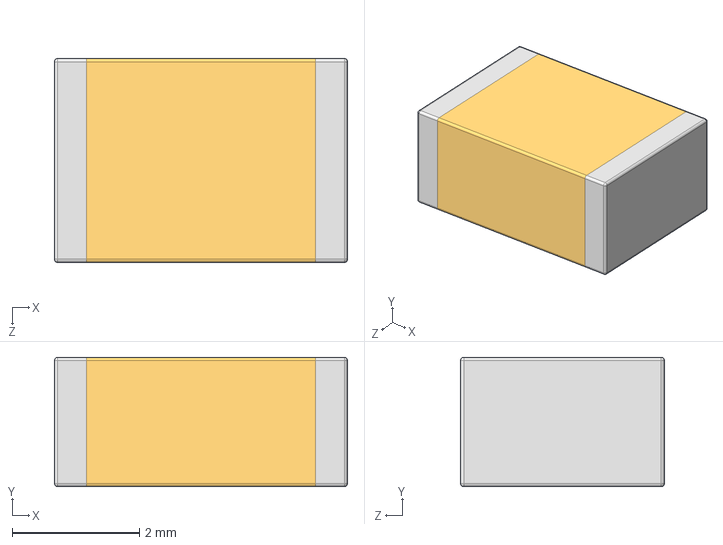
[picture p133: CAD file, 2019-04-03]
Design Documentation/3D Models/CAPC/CAPC4632X203N CDR04.step
4.60 x 2.03 x 3.20 mm
