miguel-osuna/Mikeduino-Microcontroller/Design Documentation/3D Models/CAPC/CAPC4532X155N EIA 1812.step

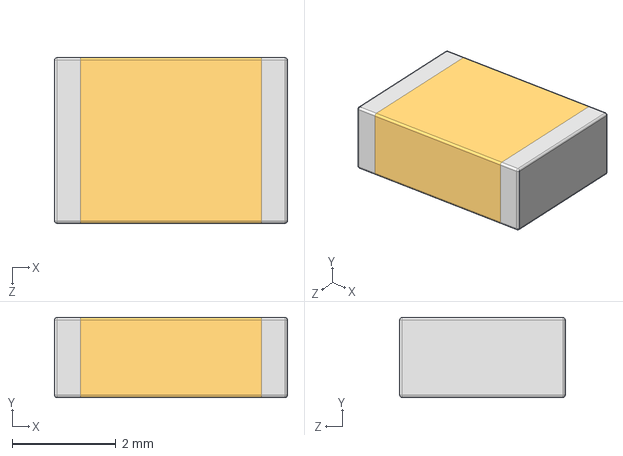
[picture p134: CAD file, 2019-04-03]
Design Documentation/3D Models/CAPC/CAPC4532X155N EIA 1812.step
4.50 x 1.55 x 3.20 mm
