miguel-osuna/Mikeduino-Microcontroller/Design Documentation/3D Models/CAPC/CAPC5764X127N EIA 2225.step

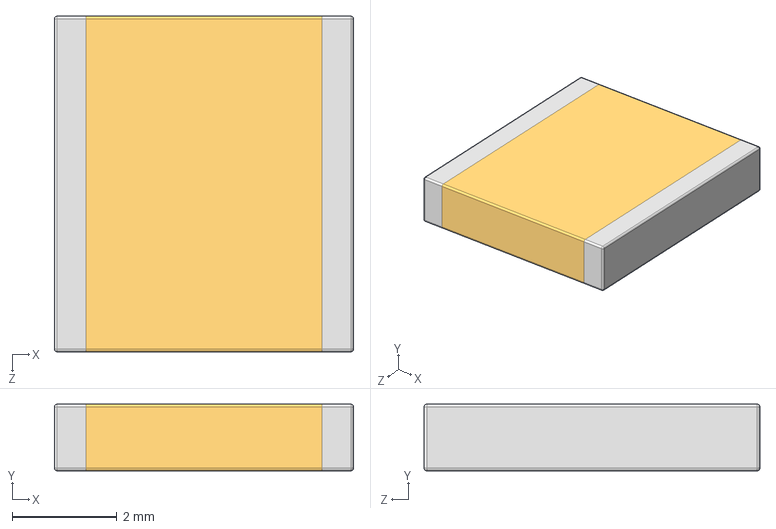
[picture p135: CAD file, 2019-04-03]
Design Documentation/3D Models/CAPC/CAPC5764X127N EIA 2225.step
5.70 x 1.27 x 6.40 mm
